flasne/Tri-de-M-Ms/SolidWorks/Raspberry/Display Connector, RPi4ModelB.SLDPRT

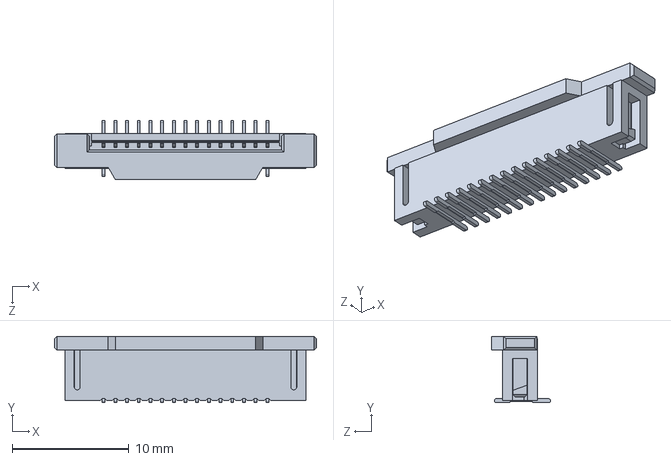
[picture p73: CAD file, 2025-01-02]
SolidWorks/Raspberry/Display Connector, RPi4ModelB.SLDPRT
22.4 x 5.68 x 5.07 mm
