flasne/Tri-de-M-Ms/SolidWorks/Raspberry/Female Micro HDMI Connector, RPi4ModelB.SLDPRT

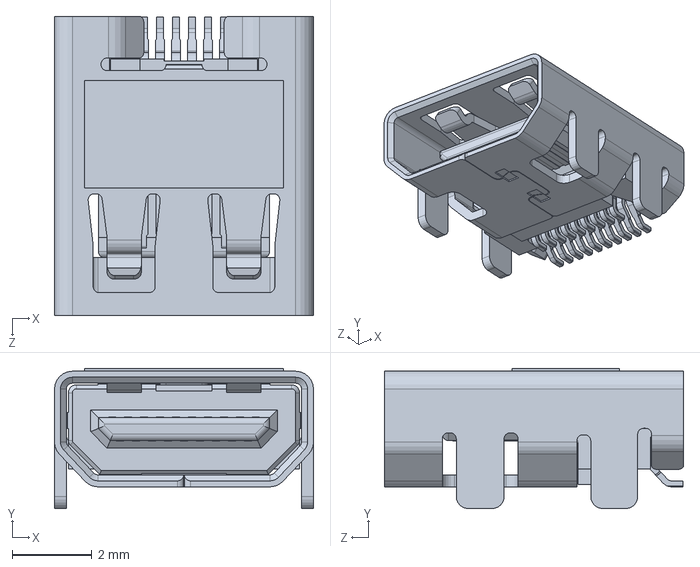
[picture p74: CAD file, 2025-01-02]
SolidWorks/Raspberry/Female Micro HDMI Connector, RPi4ModelB.SLDPRT
6.50 x 3.52 x 7.50 mm
