flasne/Tri-de-M-Ms/SolidWorks/Raspberry/PCB, RPi4ModelB.SLDPRT

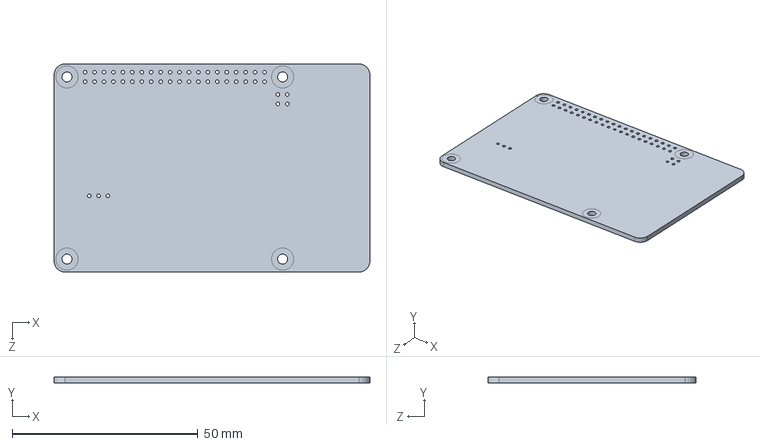
[picture p75: CAD file, 2025-01-02]
SolidWorks/Raspberry/PCB, RPi4ModelB.SLDPRT
85.0 x 1.60 x 56.0 mm
