flasne/Tri-de-M-Ms/SolidWorks/Skittle.SLDPRT

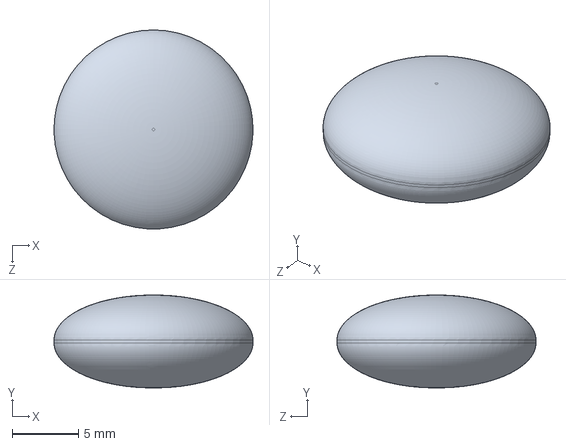
[picture p76: CAD file, 2025-01-02]
SolidWorks/Skittle.SLDPRT
15.0 x 7.00 x 15.0 mm
