flasne/Tri-de-M-Ms/SolidWorks/Raspberry/Cypress CYW43455 Wireless Module Cover, RPi4ModelB.SLDPRT

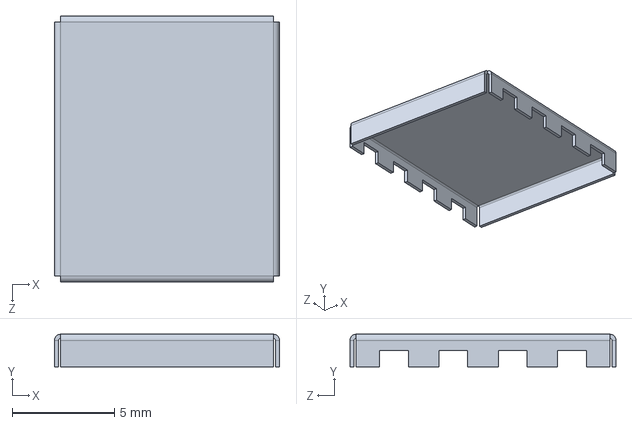
[picture p77: CAD file, 2025-01-02]
SolidWorks/Raspberry/Cypress CYW43455 Wireless Module Cover, RPi4ModelB.SLDPRT
11.0 x 1.60 x 13.0 mm
