flasne/Tri-de-M-Ms/SolidWorks/ISO - 4032 - M3 - D - N.sldprt

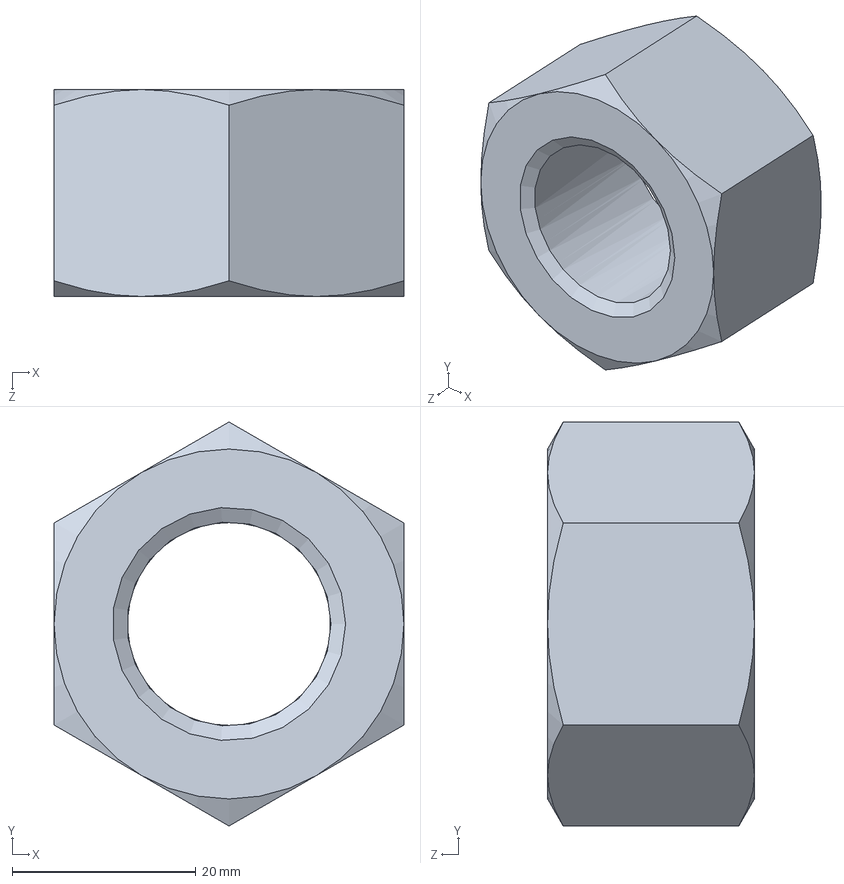
[picture p78: CAD file, 2025-01-02]
SolidWorks/ISO - 4032 - M3 - D - N.sldprt
38.1 x 44.0 x 22.5 mm
