flasne/Tri-de-M-Ms/SolidWorks/Raspberry/2.54 mm DUPONT MALE PIN HEADER, IO, 2X20, RPi4ModelB.SLDPRT

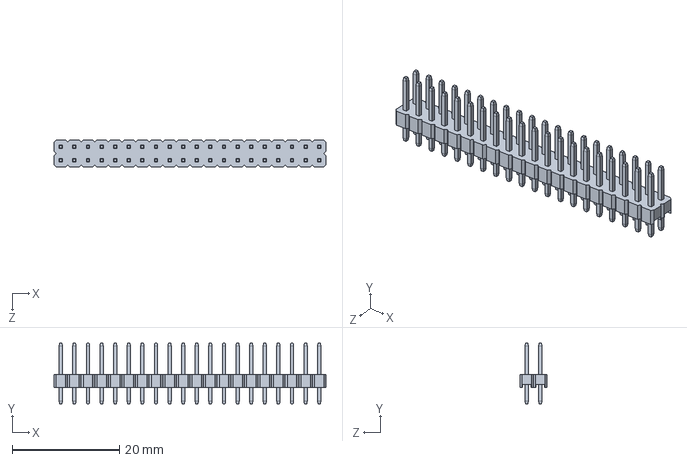
[picture p79: CAD file, 2025-01-02]
SolidWorks/Raspberry/2.54 mm DUPONT MALE PIN HEADER, IO, 2X20, RPi4ModelB.SLDPRT
50.8 x 11.3 x 5.08 mm
