flasne/Tri-de-M-Ms/SolidWorks/Raspberry/Broadcom BCM54213PE Gigabit Ethernet Transceiver, RPi4ModelB.SLDPRT

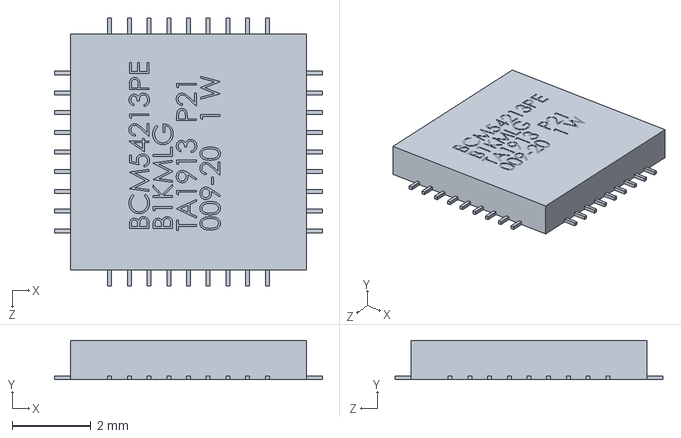
[picture p80: CAD file, 2025-01-02]
SolidWorks/Raspberry/Broadcom BCM54213PE Gigabit Ethernet Transceiver, RPi4ModelB.SLDPRT
6.80 x 1.00 x 6.80 mm
