flasne/Tri-de-M-Ms/SolidWorks/Raspberry/91D77 D9WHV 778K, 4 GB LPDDR4 SDRAM, RPi4ModelB.SLDPRT

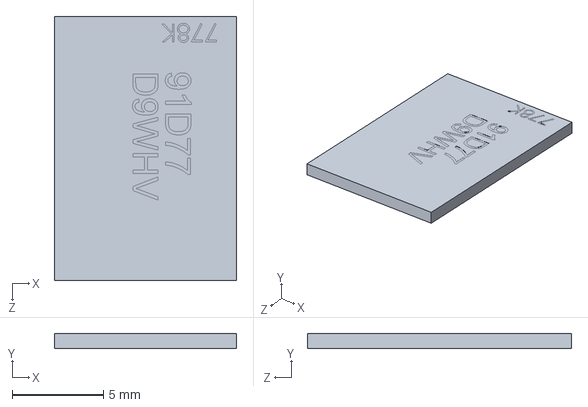
[picture p81: CAD file, 2025-01-02]
SolidWorks/Raspberry/91D77 D9WHV 778K, 4 GB LPDDR4 SDRAM, RPi4ModelB.SLDPRT
10.0 x 0.8 x 14.5 mm
