flasne/Tri-de-M-Ms/SolidWorks/Raspberry/VIA VL805 PCIe USB 3.0 controller, RPi4ModelB.SLDPRT

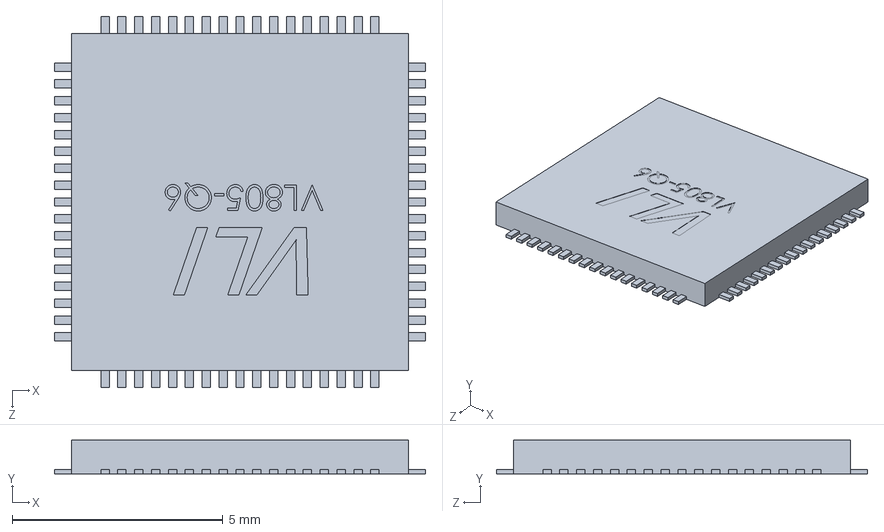
[picture p82: CAD file, 2025-01-02]
SolidWorks/Raspberry/VIA VL805 PCIe USB 3.0 controller, RPi4ModelB.SLDPRT
8.80 x 0.8 x 8.80 mm
