flasne/Tri-de-M-Ms/SolidWorks/Raspberry/MxL7704 Universal PMIC, RPi4ModelB.SLDPRT

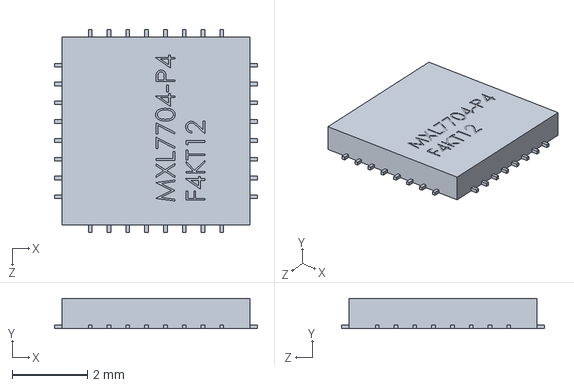
[picture p83: CAD file, 2025-01-02]
SolidWorks/Raspberry/MxL7704 Universal PMIC, RPi4ModelB.SLDPRT
5.40 x 0.8 x 5.40 mm
