flasne/Tri-de-M-Ms/SolidWorks/Servo Motor Link.SLDPRT

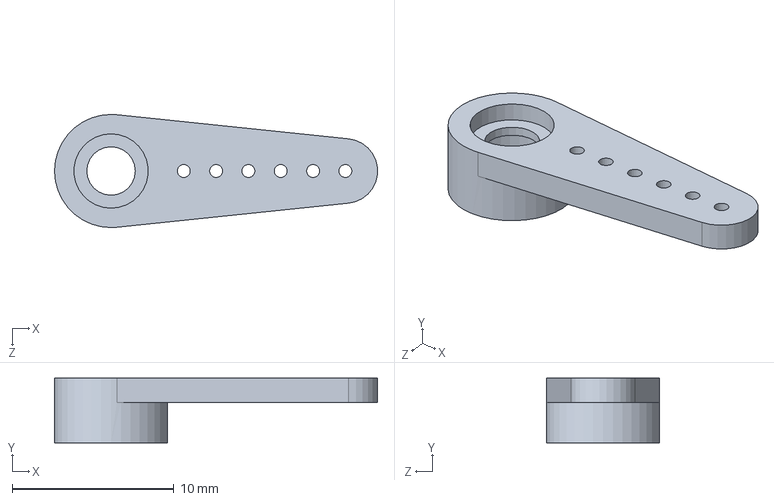
[picture p84: CAD file, 2025-01-02]
SolidWorks/Servo Motor Link.SLDPRT
20.0 x 4.00 x 7.00 mm
