flasne/Tri-de-M-Ms/SolidWorks/Raspberry/SD Card Slot, RPi4ModelB.SLDPRT

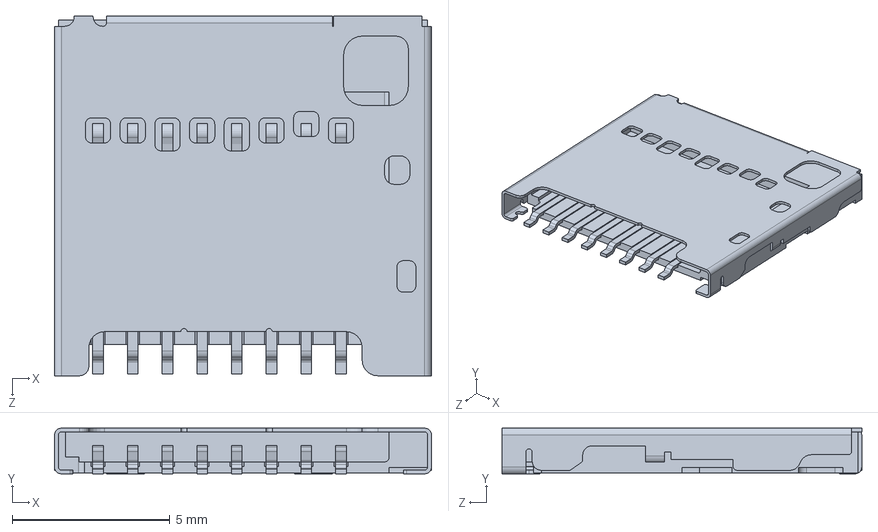
[picture p85: CAD file, 2025-01-02]
SolidWorks/Raspberry/SD Card Slot, RPi4ModelB.SLDPRT
11.9 x 1.45 x 11.4 mm
