flasne/Tri-de-M-Ms/SolidWorks/Raspberry/Female USB Type C Connector, RPi4ModelB.SLDPRT

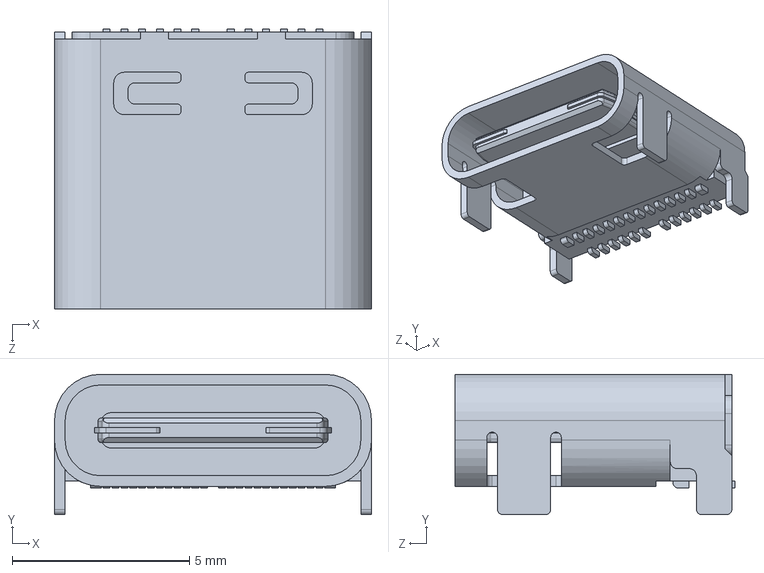
[picture p86: CAD file, 2025-01-02]
SolidWorks/Raspberry/Female USB Type C Connector, RPi4ModelB.SLDPRT
8.94 x 3.96 x 7.90 mm
