flasne/Tri-de-M-Ms/SolidWorks/Grove-infrared-digital-temperature-sensor.step

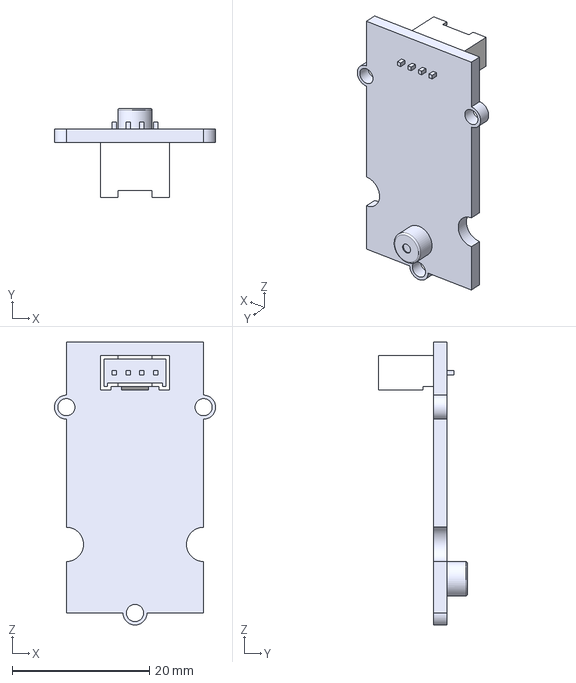
[picture p87: CAD file, 2025-01-02]
SolidWorks/Grove-infrared-digital-temperature-sensor.step
23.5 x 13.0 x 41.3 mm
