flasne/Tri-de-M-Ms/SolidWorks/Raspberry/Microphone Plug, RPi4ModelB.SLDPRT

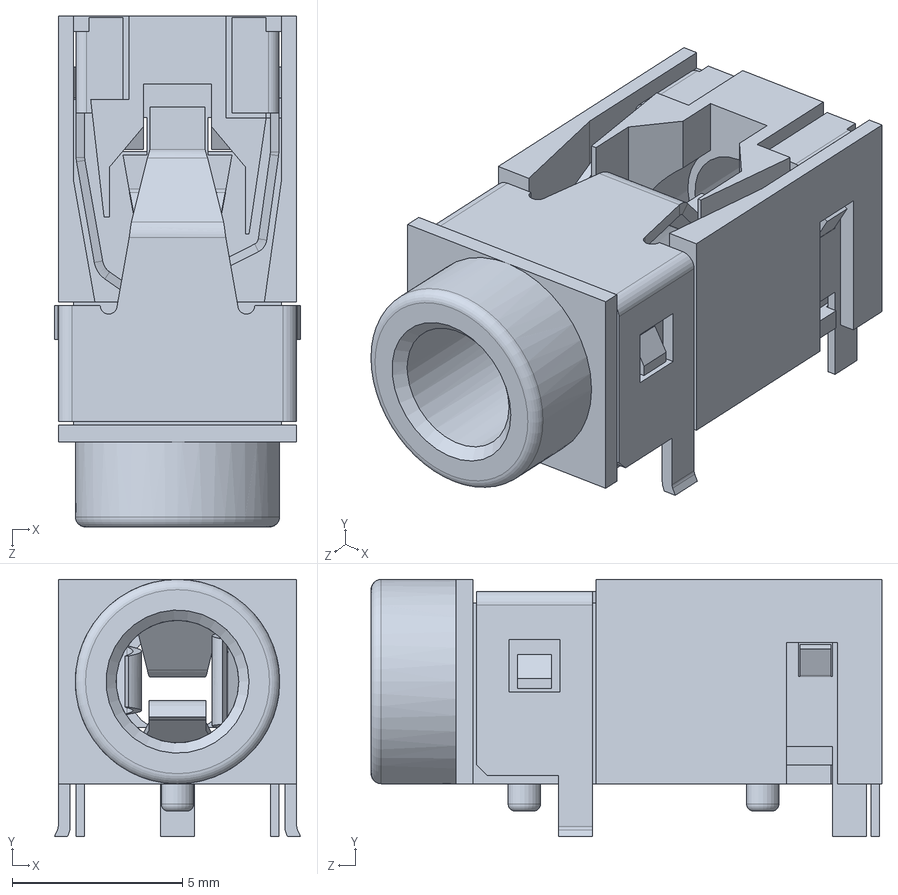
[picture p88: CAD file, 2025-01-02]
SolidWorks/Raspberry/Microphone Plug, RPi4ModelB.SLDPRT
7.23 x 7.55 x 15.0 mm
