flasne/Tri-de-M-Ms/SolidWorks/Raspberry/2.54 mm DUPONT MALE PIN HEADER, POE, 2X2, RPi4ModelB.SLDPRT

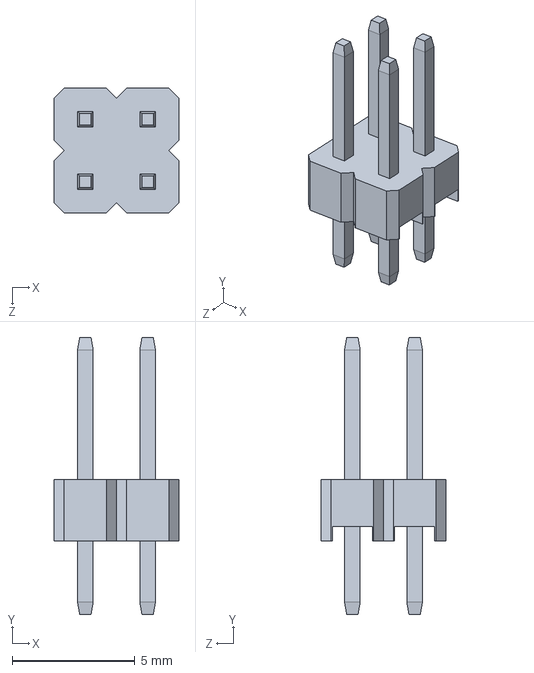
[picture p89: CAD file, 2025-01-02]
SolidWorks/Raspberry/2.54 mm DUPONT MALE PIN HEADER, POE, 2X2, RPi4ModelB.SLDPRT
5.08 x 11.3 x 5.08 mm
