flasne/Tri-de-M-Ms/SolidWorks/plaque d'entrainement.SLDPRT

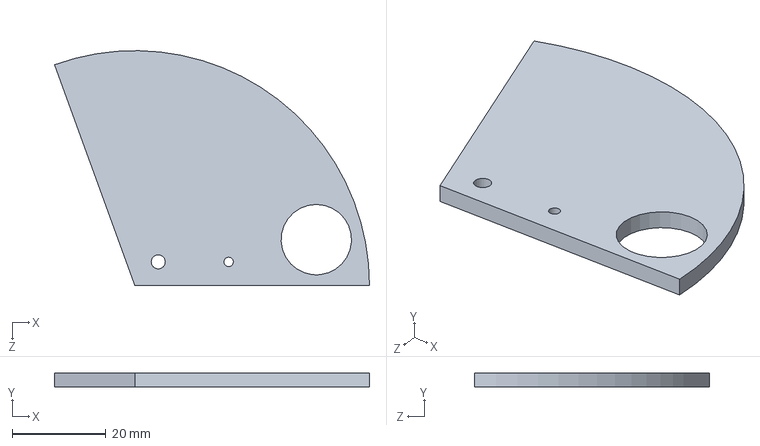
[picture p90: CAD file, 2025-01-02]
SolidWorks/plaque d'entrainement.SLDPRT
67.1 x 3.00 x 50.0 mm
