flasne/Tri-de-M-Ms/SolidWorks/Servo Motor.SLDPRT

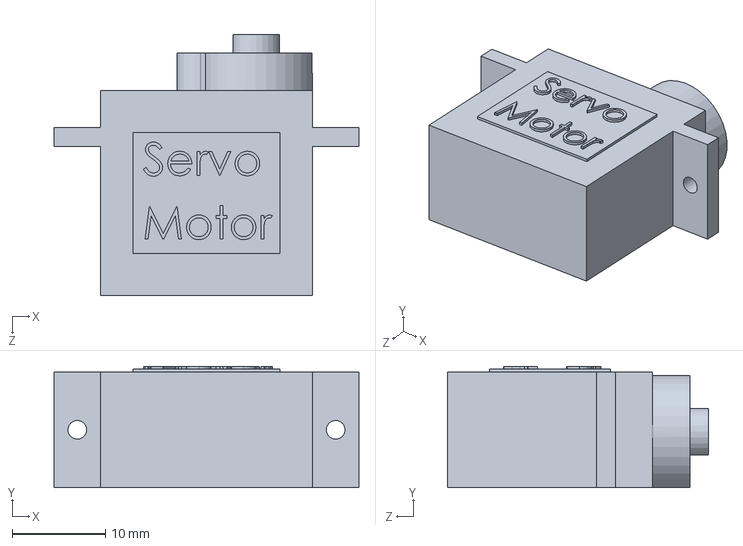
[picture p91: CAD file, 2025-01-02]
SolidWorks/Servo Motor.SLDPRT
32.7 x 13.0 x 28.0 mm
