flasne/Tri-de-M-Ms/SolidWorks/goulotte de stockage.SLDPRT

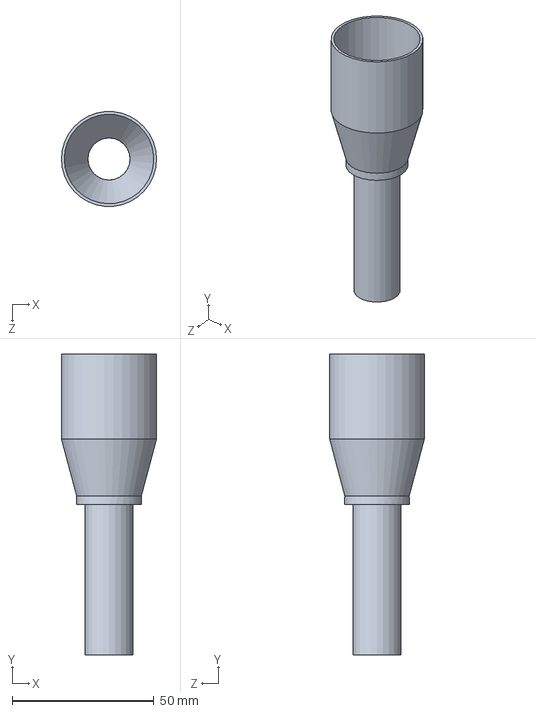
[picture p92: CAD file, 2025-01-02]
SolidWorks/goulotte de stockage.SLDPRT
33.5 x 106.0 x 33.4 mm
