flasne/Tri-de-M-Ms/SolidWorks/Grove digital infrared temperature sensor.stl

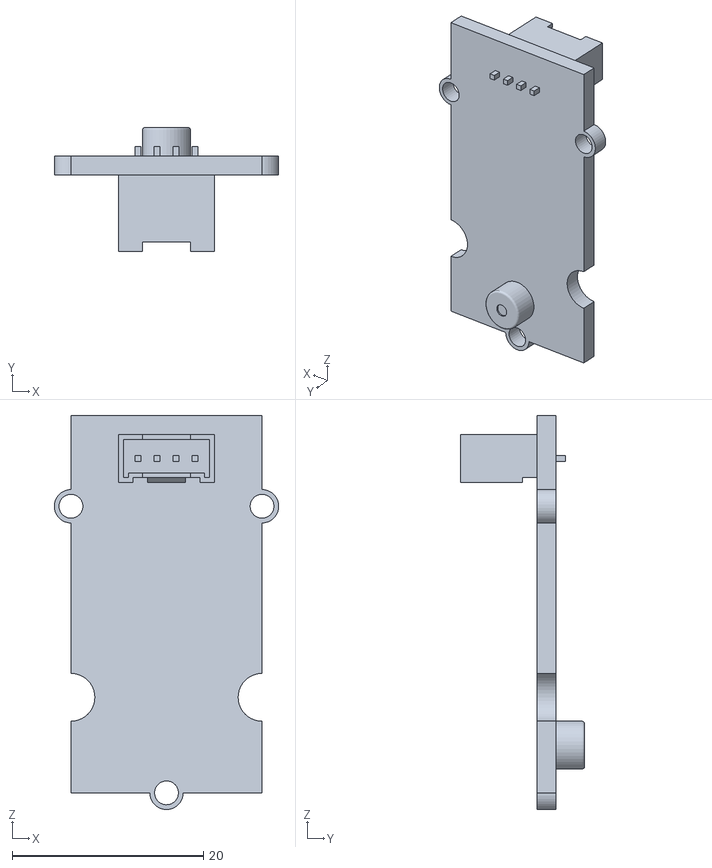
[picture p93: CAD file, 2025-01-02]
SolidWorks/Grove digital infrared temperature sensor.stl
23.5 x 13.0 x 41.2
