flasne/Tri-de-M-Ms/SolidWorks/TCS3200 Sensor 3D Model.SLDPRT

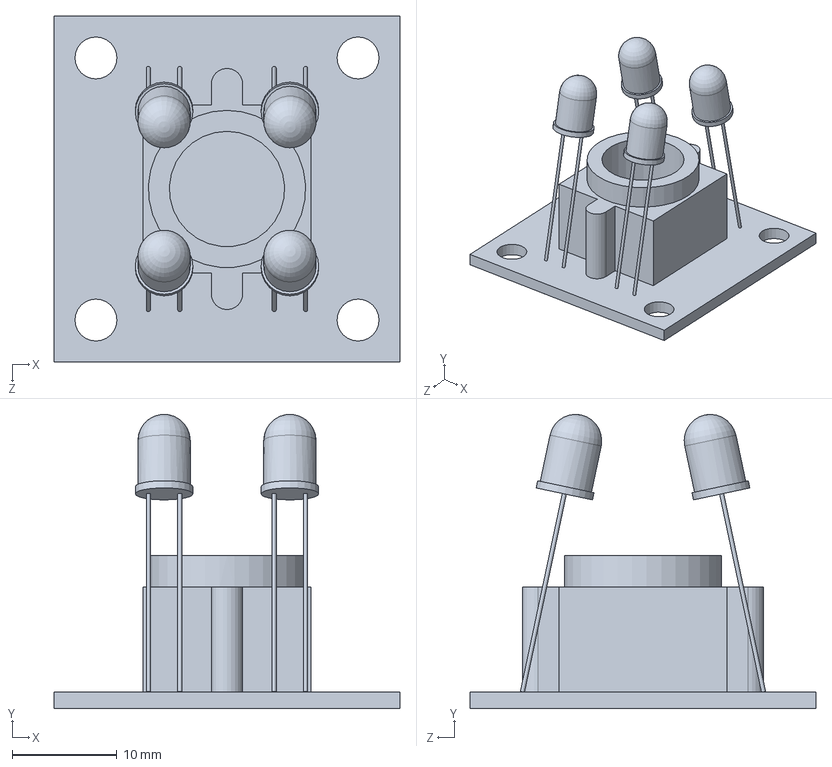
[picture p94: CAD file, 2025-01-02]
SolidWorks/TCS3200 Sensor 3D Model.SLDPRT
33.0 x 28.1 x 33.0 mm
