flasne/Tri-de-M-Ms/SolidWorks/Support de capteur.SLDPRT

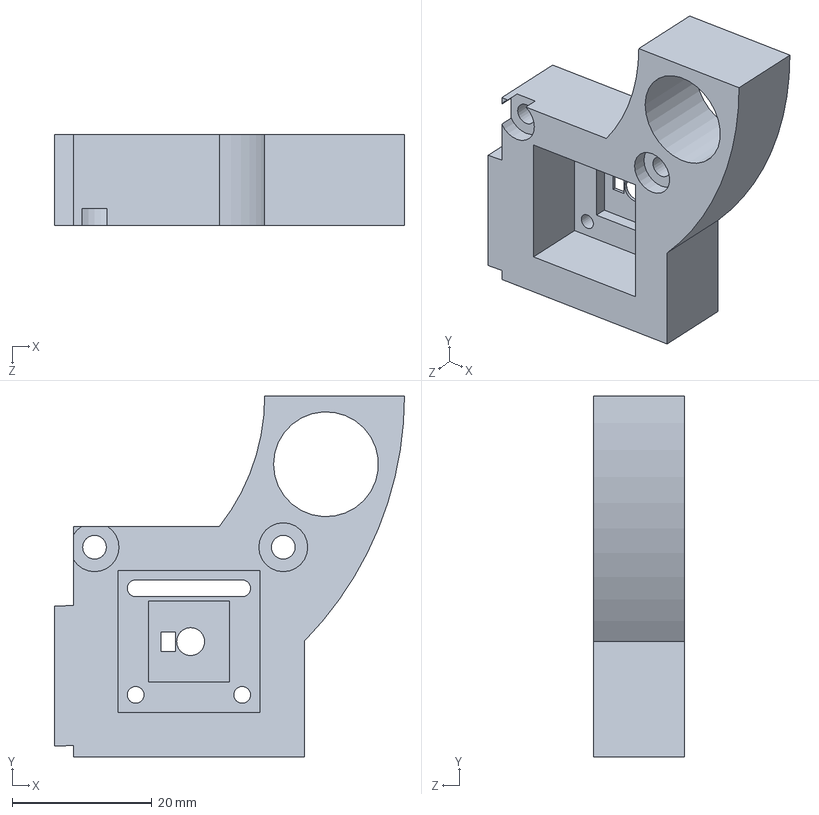
[picture p95: CAD file, 2025-01-02]
SolidWorks/Support de capteur.SLDPRT
50.1 x 51.6 x 13.0 mm
